ceybers/spline36-keyboard/images/inspiration/tbk-by-bastardkb.jpg

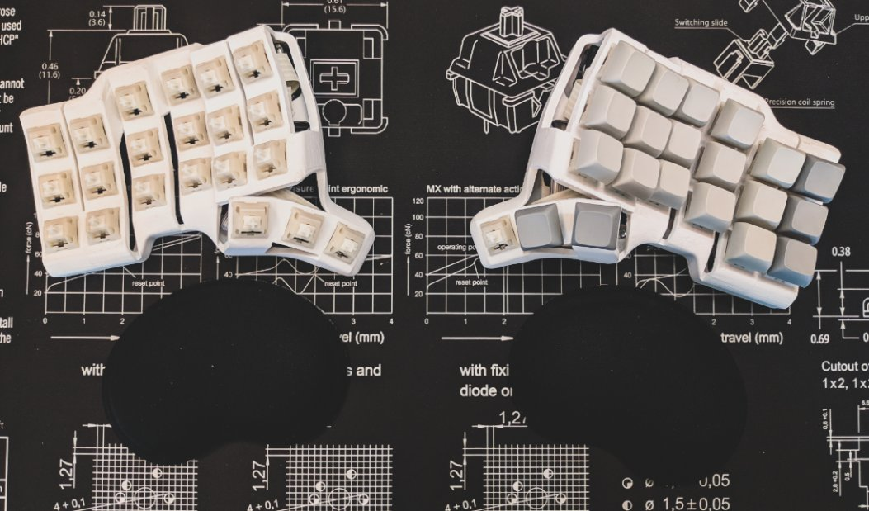
images/inspiration/tbk-by-bastardkb.jpg
