ceybers/spline36-keyboard/images/photos/IMG_20240826_093114.jpg

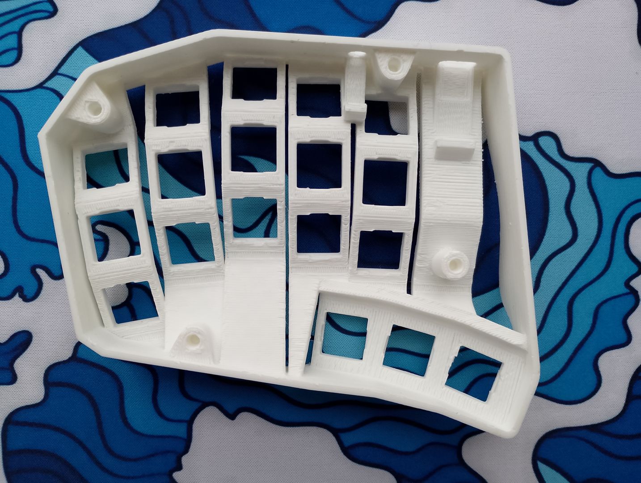
images/photos/IMG_20240826_093114.jpg
