ceybers/spline36-keyboard/images/photos/IMG_20240826_093411.jpg

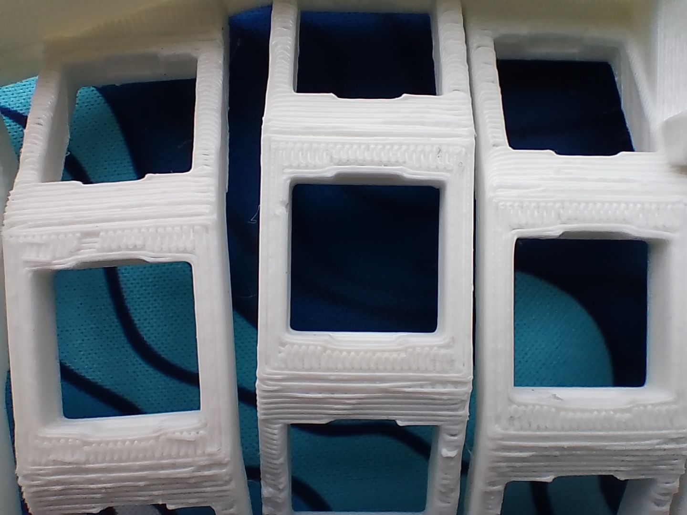
images/photos/IMG_20240826_093411.jpg
