ceybers/spline36-keyboard/images/photos/IMG_20240826_094537.jpg

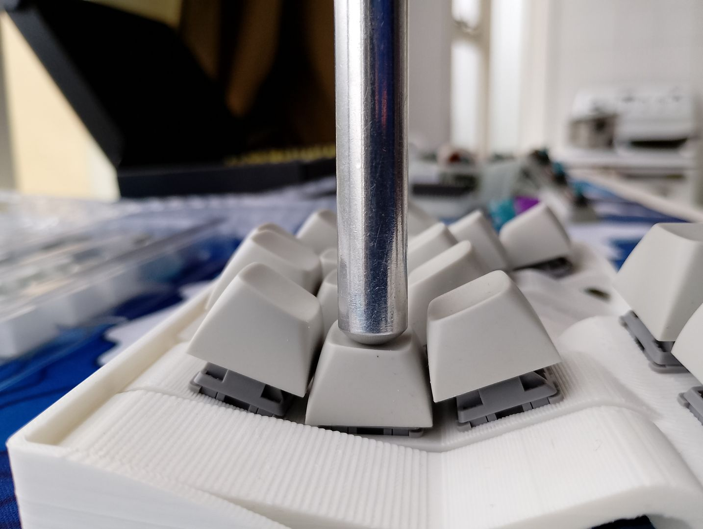
images/photos/IMG_20240826_094537.jpg
