ceybers/spline36-keyboard/kle/keyboard-layout-202408231540.png

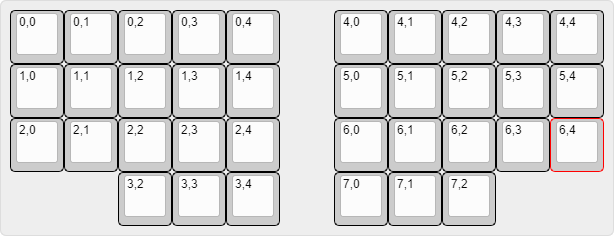
kle/keyboard-layout-202408231540.png
